MaxStrange/Home_Security_System/HSS_node_accumulator/accumulator_0_2/sender/sender.ino

/**
This is the sender node for the 0.1 version of the accumulator.
*/
#include <SPI.h>
#include "RF24.h"

/**Constants**/
const uint16_t THREAT_SIGNAL = 0x1BA0;
const uint16_t DISARM_SIGNAL = 0x1151;

/**Pin declarations**/
const int RADIO_PIN_1 = 9;
const int RADIO_PIN_2 = 10;

/**Radio code**/
RF24 radio(RADIO_PIN_1, RADIO_PIN_2);
byte node_ids[][6] = { "cmltr", "sensr" };

void setup(void)
{
  Serial.begin(115200);
  
  /**Radio**/
  radio.begin();
  radio.setRetries(15, 15);
  radio.openWritingPipe(node_ids[1]);
  radio.startListening();
}

void loop(void)
{
  Serial.println("Starting to send.");
  delay(1000);
  Serial.println("Sending threat.");
  send_signal(THREAT_SIGNAL);
  delay(4000);
  Serial.println("Sending threat.");
  send_signal(THREAT_SIGNAL);
  delay(4000);
  Serial.println("Sending disarm.");
  send_signal(DISARM_SIGNAL);
  delay(10000);
  Serial.println("Sending threat.");
  send_signal(THREAT_SIGNAL);
  delay(3000);
  Serial.println("Sending disarm.");
  send_signal(DISARM_SIGNAL);
  delay(2000);
  Serial.println("Sending threat.");
  send_signal(THREAT_SIGNAL);
  delay(8000);
  Serial.println("Sending threat.");
  send_signal(THREAT_SIGNAL);
  delay(10000);
  Serial.println("Sending threat.");
  send_signal(THREAT_SIGNAL);
  delay(2000);
  Serial.println("Sending threat.");
  send_signal(THREAT_SIGNAL);
  delay(2000);
  Serial.println("Sending disarm.");
  send_signal(DISARM_SIGNAL);
  delay(5000);
}

void send_signal(uint16_t to_send)
{
  radio.stopListening();
  radio.write(&to_send, sizeof(uint16_t));
  radio.startListening();
}
