MaxStrange/Home_Security_System/RFID_test/IDLA20/IDLA20_sleep_fix/IDLA20_sleep_fix.ino

#include <avr/interrupt.h>
#include <avr/power.h>
#include <avr/sleep.h>
#include <avr/io.h>
#include <SPI.h>
#include "RF24.h"

const int LED = 8;

boolean something_to_read = false;
void read_key_ISR(void)
{
  detachInterrupt(0);
  something_to_read = true;
}

void go_to_sleep(void)
{
  //WORKS! Only IDLE...
  set_sleep_mode(SLEEP_MODE_IDLE);//set_sleep_mode(SLEEP_MODE_STANDBY);
  sleep_enable();
  sleep_mode();
}

String inputString = "";         // a string to hold incoming data
boolean stringComplete = false;  // whether the string is complete

const int KEY_LENGTH = 16;
char key_a[KEY_LENGTH] = { 63, 100, 94, 230, 166, 102, 230, 76, 102, 166, 201, 201, 202, 214, 242, 0 };
char key_b[KEY_LENGTH] = { 63, 100, 94, 230, 166, 102, 166, 76, 153, 166, 76, 153, 202, 214, 242, 0 };
char key_c[KEY_LENGTH] = { 63, 100, 94, 230, 166, 166, 204, 151, 204, 201, 62, 234, 202, 214, 242, 0 };
char incoming_key[KEY_LENGTH] = { 0,0,0,0,0,0,0,0,0,0,0,0,0,0,0,0 };


void setup()
{
   Serial.begin(9600);
   inputString.reserve(20);
   pinMode(LED, OUTPUT);
}

void loop()
{
  if (something_to_read)
     serialEvent();
   
   if (stringComplete)
   {
     Serial.println(inputString);
     
     inputString.toCharArray(incoming_key, KEY_LENGTH);
     
     boolean known = true;
     for (int i = 0; i < KEY_LENGTH; i++)
     {
       if ((incoming_key[i] != key_a[i]) && (incoming_key[i] != key_b[i]) && (incoming_key[i] != key_c[i]))
       {
         known = false;
         break;
       }
     }
     
     if (known)
       Serial.println("KNOWN");
     else
       Serial.println("UNKOWN");
     
     inputString = "";
     stringComplete = false;
   }
   attachInterrupt(0, read_key_ISR, LOW);
   delay(500);
   go_to_sleep();
   delay(500);
}

/*
  SerialEvent occurs whenever a new data comes in the
  hardware serial RX.  This routine is run between each
  time loop() runs, so using delay inside loop can delay
  response.  Multiple bytes of data may be available.
  */
void serialEvent()
{
   while (Serial.available())
   {
     char inChar = (char)Serial.read();  
     inputString += inChar;
     
     if (inChar == 0)
     {
       stringComplete = true;
     }
   }
   something_to_read = false;
}
