MaxStrange/Home_Security_System/nRF_tests/nRF_interrupt_test/nRF_interrupt_test.ino

/**
This sketch is identical to the receiver in the three node topology
except that it uses interrupts to listen for signals rather than
polling.

First it waits 3 seconds, then it broadcasts the system_armed message.
Then it listens to the other two nodes
and reacts accordingly (lights its red LED when intruder alert, green otherwise). It doesn't
send any response back though (at least not in this version).
*/
#include <SPI.h>
#include "RF24.h"

/**Pin declarations*/
const unsigned int RED = 8;
const unsigned int GREEN = 6;

/**Radio code*/
const int TIMEOUT = 200;//ms to wait for timeout
RF24 radio(9,10);  // Set up nRF24L01 radio on SPI bus plus pins 9 & 10 
byte talking_pipes[][6] = { "1Node", "2Node" };
byte broadcast_pipes[][6] = { "Node1", "Node2" };

volatile bool pipe1_alert = false;
volatile bool pipe2_alert = false;
bool have_not_broadcasted = true;

volatile int blah_count = 0;

void setup(void)
{
  /**Pin sets*/
  pinMode(GREEN, OUTPUT);
  pinMode(RED, OUTPUT);
    
  /**Radio*/
  radio.begin();
  radio.setRetries(15, 15);
  radio.openReadingPipe(1, talking_pipes[0]);
  radio.openReadingPipe(2, talking_pipes[1]);
  radio.startListening();
  
  Serial.begin(9600);
}

void loop(void)
{
  delay(500);
  Serial.println("Loop");
  if (have_not_broadcasted)
  {
    Serial.println("Broadcasting.");
    for (int i = 0; i < 15; i++)
      broadcast();
      
    have_not_broadcasted = false;
    Serial.println("Attaching ISR");
    attachInterrupt(0, check_messages_ISR, LOW);
  }
  
  display_alert_status();
}

void broadcast(void)
{
  Serial.println("Stop listening.");
  radio.stopListening();
  
  for (int i = 0; i < 2; i++)
  {
    Serial.println("Open writing pipe.");
    radio.openWritingPipe(broadcast_pipes[i]);
    bool arm_system = true;
    Serial.println("Write.");
    radio.write(&arm_system, sizeof(bool));
  }
  
  Serial.println("Start listening again.");
  radio.startListening();
}

void check_messages_ISR(void)
{
  bool tx, fail, rx;
  radio.whatHappened(tx, fail, rx);
  
  bool intruder_alert = (pipe1_alert || pipe2_alert);
  uint8_t pipe_number;
  if (rx && radio.available(&pipe_number))
  {
    Serial.println("RX");
    radio.read(&intruder_alert, sizeof(bool));
  }
  
  if (fail)
    Serial.println("FAIL");
    
  if (tx)
    Serial.println("TX");
  
  switch (pipe_number)
  {
    case 1://pipe 1
      pipe1_alert = intruder_alert;
      if (intruder_alert) Serial.println("Pipe 1 alert!"); else Serial.println("Pipe 1 clear.");
      break;
    case 2://pipe 2
      pipe2_alert = intruder_alert;
      if (intruder_alert) Serial.println("Pipe 2 alert!"); else Serial.println("Pipe 2 clear.");
      break;
  }
}

void display_alert_status(void)
{
  if (pipe1_alert || pipe2_alert)
  {
    digitalWrite(GREEN, LOW);
    digitalWrite(RED, HIGH);
  }
  else
  {
    digitalWrite(GREEN, HIGH);
    digitalWrite(RED, LOW);
  }
}
